ARTS-Laboratory/IoT-Water-Level-Sensor/system_development/Cellular/v0.2/Custom PCB's/Power PCB/README.md

# Power Board

These are the KiCad files used to create the power PCB.

## .SCH 
This is the electrical wiring diagram for the PCB. This file contains links to the datasheets for all components used in the PCB.

## .PCB
This is the file for creating the physical PCB (as well as offering a 3D render of the PCB)
