ARTS-Laboratory/IoT-Water-Level-Sensor/system_development/Cellular/v0.1/field tests/04_21-04_22/usgs_data.csv

 |  | date | time |  |  |  | stage | temperature
USGS | 2169000 | 4/21/2022 | 15:30 | EDT | 5.97 | 154.63 | 155 | 14.9
USGS | 2169000 | 4/21/2022 | 15:45 | EDT | 5.93 | 154.59 | 154.96 | 14.8
USGS | 2169000 | 4/21/2022 | 16:00 | EDT | 5.91 | 154.57 | 154.94 | 14.8
USGS | 2169000 | 4/21/2022 | 16:15 | EDT | 5.88 | 154.54 | 154.91 | 14.8
USGS | 2169000 | 4/21/2022 | 16:30 | EDT | 5.86 | 154.52 | 154.89 | 14.8
USGS | 2169000 | 4/21/2022 | 16:45 | EDT | 5.83 | 154.49 | 154.86 | 14.7
USGS | 2169000 | 4/21/2022 | 17:00 | EDT | 5.82 | 154.48 | 154.85 | 14.7
USGS | 2169000 | 4/21/2022 | 17:15 | EDT | 5.81 | 154.47 | 154.84 | 14.7
USGS | 2169000 | 4/21/2022 | 17:30 | EDT | 5.79 | 154.45 | 154.82 | 14.6
USGS | 2169000 | 4/21/2022 | 17:45 | EDT | 5.78 | 154.44 | 154.81 | 14.6
USGS | 2169000 | 4/21/2022 | 18:00 | EDT | 5.77 | 154.43 | 154.8 | 14.6
USGS | 2169000 | 4/21/2022 | 18:15 | EDT | 5.77 | 154.43 | 154.8 | 14.5
USGS | 2169000 | 4/21/2022 | 18:30 | EDT | 5.76 | 154.42 | 154.79 | 14.5
USGS | 2169000 | 4/21/2022 | 18:45 | EDT | 5.76 | 154.42 | 154.79 | 14.4
USGS | 2169000 | 4/21/2022 | 19:00 | EDT | 5.75 | 154.41 | 154.78 | 14.4
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
