ARTS-Laboratory/IoT-Water-Level-Sensor/system_development/Cellular/v0.1/field tests/05_03-05_09/stage_data.csv

 |  |  | date | time |  |  | value | adaptive index | adaptive value
0F0NJQPDRJXMENSYHWX61DW5M4 | 153 | 1793320 | 5/3/2022 | 9:39:42 AM | 13:39:42 | UTC | 153 | 1 | 153 | 0
0F0NJT7999G4E5HH99HHKH4P6C | 153 | 1793320 | 5/3/2022 | 9:44:07 AM | 13:44:07 | UTC | 153 | 2 | 153 | 0
0F0NJXPKSRJBQ8WAA7AC0D6Y2S | 153.25 | 1793320 | 5/3/2022 | 9:50:12 AM | 13:50:12 | UTC | 153.25 | 3 | 153.25 | 0
0F0NJZP8HF8RG365QKV08D1JWJ | 152.42 | 1793320 | 5/3/2022 | 9:53:41 AM | 13:53:41 | UTC | 152.42 | 4 | 152.42 | 0
0F0NM4R60VDQANZM3WNMMC0HX7 | 153 | 1793320 | 5/3/2022 | 10:58:27 AM | 14:58:27 | UTC | 153 | 5 | 153 | 0
0F0NM769279931YKHYYXZYRMA1 | 153 | 1793320 | 5/3/2022 | 11:02:42 AM | 15:02:42 | UTC | 153 | 6 | 153 | 0
0F0NM7P03MXMFY87XH234CH9K3 | 153 | 1793320 | 5/3/2022 | 11:03:34 AM | 15:03:34 | UTC | 153 | 7 | 153 | 0
0F0NMA3SWRW5TD514BHWAYF0Z5 | 153 | 1793320 | 5/3/2022 | 11:07:49 AM | 15:07:49 | UTC | 153 | 11 | 153 | 0
0F0NMCB0VVYKTFTS1PY2FKWZX7 | 153 | 1793320 | 5/3/2022 | 11:11:42 AM | 15:11:42 | UTC | 153 | 15 | 153 | 0
0F0NMEKFHNVDS8CANYTDE6VJWJ | 153 | 1793320 | 5/3/2022 | 11:15:40 AM | 15:15:40 | UTC | 153 | 19 | 153 | 0
0F0NMGWXJBT11FHRV2F50JVWW0 | 153 | 1793320 | 5/3/2022 | 11:19:40 AM | 15:19:40 | UTC | 153 | 23 | 153 | 0
0F0NMK5Y89X48QQDZEPRES7CVD | 153 | 1793320 | 5/3/2022 | 11:23:40 AM | 15:23:40 | UTC | 153 | 27 | 153 | 0
0F0NMNF5AP266YJV44F9623FB0 | 153 | 1793320 | 5/3/2022 | 11:27:40 AM | 15:27:40 | UTC | 153 | 31 | 153 | 0
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
0F0R3JME0WJ84MVRCA2KWJHB8K | 152.08 | 1793320 | 5/6/2022 | 1:00:42 PM | 17:00:42 | UTC | 153 |  |  | 0.92
0F0R3MXW04BC4MDB38EVNZ0SR5 | 152.08 | 1793320 | 5/6/2022 | 1:04:43 PM | 17:04:43 | UTC | 153 |  |  | 0.92
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
