ARTS-Laboratory/IoT-Water-Level-Sensor/system_development/Cellular/v0.1/field tests/05_03-05_09/usgs_data.csv

 |  | date | time |  |  | stage | temperature
USGS | 2169000 | 5/3/2022 | 9:30 | EDT | 3.97 | 153 | 15.3
USGS | 2169000 | 5/3/2022 | 9:45 | EDT | 3.97 | 153 | 15.3
USGS | 2169000 | 5/3/2022 | 10:00 | EDT | 3.97 | 153 | 15.3
USGS | 2169000 | 5/3/2022 | 10:15 | EDT | 3.97 | 153 | 15.4
USGS | 2169000 | 5/3/2022 | 10:30 | EDT | 3.97 | 153 | 15.4
USGS | 2169000 | 5/3/2022 | 10:45 | EDT | 3.97 | 153 | 15.5
USGS | 2169000 | 5/3/2022 | 11:00 | EDT | 3.97 | 153 | 15.6
USGS | 2169000 | 5/3/2022 | 11:15 | EDT | 3.97 | 153 | 15.6
USGS | 2169000 | 5/3/2022 | 11:30 | EDT | 3.97 | 153 | 15.7
USGS | 2169000 | 5/3/2022 | 11:45 | EDT | 3.97 | 153 | 15.7
USGS | 2169000 | 5/3/2022 | 12:00 | EDT | 3.97 | 153 | 15.8
USGS | 2169000 | 5/3/2022 | 12:15 | EDT | 3.97 | 153 | 15.9
USGS | 2169000 | 5/3/2022 | 12:30 | EDT | 3.97 | 153 | 16
USGS | 2169000 | 5/3/2022 | 12:45 | EDT | 3.96 | 152.99 | 16
USGS | 2169000 | 5/3/2022 | 13:00 | EDT | 3.97 | 153 | 16.1
USGS | 2169000 | 5/3/2022 | 13:15 | EDT | 3.97 | 153 | 16.1
USGS | 2169000 | 5/3/2022 | 13:30 | EDT | 3.97 | 153 | 16.2
USGS | 2169000 | 5/3/2022 | 13:45 | EDT | 3.97 | 153 | 16.2
USGS | 2169000 | 5/3/2022 | 14:00 | EDT | 3.97 | 153 | 16.3
USGS | 2169000 | 5/3/2022 | 14:15 | EDT | 3.97 | 153 | 16.3
USGS | 2169000 | 5/3/2022 | 14:30 | EDT | 3.97 | 153 | 16.4
USGS | 2169000 | 5/3/2022 | 14:45 | EDT | 3.97 | 153 | 16.4
USGS | 2169000 | 5/3/2022 | 15:00 | EDT | 3.97 | 153 | 16.4
USGS | 2169000 | 5/3/2022 | 15:15 | EDT | 3.99 | 153.02 | 16.4
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
USGS | 2169000 | 5/9/2022 | 21:00 | EDT | 2.75 | 151.78 | 16.5
USGS | 2169000 | 5/9/2022 | 21:15 | EDT | 2.76 | 151.79 | 16.5
USGS | 2169000 | 5/9/2022 | 21:30 | EDT | 2.76 | 151.79 | 16.5
USGS | 2169000 | 5/9/2022 | 21:45 | EDT | 2.77 | 151.8 | 16.5
USGS | 2169000 | 5/9/2022 | 22:00 | EDT | 2.77 | 151.8 | 16.5
USGS | 2169000 | 5/9/2022 | 22:15 | EDT | 2.78 | 151.81 | 16.5
USGS | 2169000 | 5/9/2022 | 22:30 | EDT | 2.78 | 151.81 | 16.5
USGS | 2169000 | 5/9/2022 | 22:45 | EDT | 2.78 | 151.81 | 16.5
USGS | 2169000 | 5/9/2022 | 23:00 | EDT | 2.78 | 151.81 | 16.4
USGS | 2169000 | 5/9/2022 | 23:15 | EDT | 2.78 | 151.81 | 16.4
