ARTS-Laboratory/IoT-Water-Level-Sensor/system_development/Cellular/v0.1/field tests/04_06-04_07/usgs_data.csv

 |  | date | time |  |  | stage
USGS | 2169506 | 4/6/2022 | 14:15 | EDT | 1.06 | 168.06 | P
USGS | 2169506 | 4/6/2022 | 14:30 | EDT | 1.06 | 168.06 | P
USGS | 2169506 | 4/6/2022 | 14:45 | EDT | 1.06 | 168.06 | P
USGS | 2169506 | 4/6/2022 | 15:00 | EDT | 1.05 | 168.05 | P
USGS | 2169506 | 4/6/2022 | 15:15 | EDT | 1.05 | 168.05 | P
USGS | 2169506 | 4/6/2022 | 15:30 | EDT | 1.06 | 168.06 | P
USGS | 2169506 | 4/6/2022 | 15:45 | EDT | 1.05 | 168.05 | P
USGS | 2169506 | 4/6/2022 | 16:00 | EDT | 1.06 | 168.06 | P
USGS | 2169506 | 4/6/2022 | 16:15 | EDT | 1.05 | 168.05 | P
USGS | 2169506 | 4/6/2022 | 16:30 | EDT | 1.06 | 168.06 | P
USGS | 2169506 | 4/6/2022 | 16:45 | EDT | 1.06 | 168.06 | P
USGS | 2169506 | 4/6/2022 | 17:00 | EDT | 1.06 | 168.06 | P
USGS | 2169506 | 4/6/2022 | 17:15 | EDT | 1.06 | 168.06 | P
USGS | 2169506 | 4/6/2022 | 17:30 | EDT | 1.06 | 168.06 | P
USGS | 2169506 | 4/6/2022 | 17:45 | EDT | 1.06 | 168.06 | P
USGS | 2169506 | 4/6/2022 | 18:00 | EDT | 1.05 | 168.05 | P
USGS | 2169506 | 4/6/2022 | 18:15 | EDT | 1.06 | 168.06 | P
USGS | 2169506 | 4/6/2022 | 18:30 | EDT | 1.12 | 168.12 | P
USGS | 2169506 | 4/6/2022 | 18:45 | EDT | 1.18 | 168.18 | P
USGS | 2169506 | 4/6/2022 | 19:00 | EDT | 1.23 | 168.23 | P
USGS | 2169506 | 4/6/2022 | 19:15 | EDT | 1.44 | 168.44 | P
USGS | 2169506 | 4/6/2022 | 19:30 | EDT | 1.51 | 168.51 | P
USGS | 2169506 | 4/6/2022 | 19:45 | EDT | 1.62 | 168.62 | P
USGS | 2169506 | 4/6/2022 | 20:00 | EDT | 1.96 | 168.96 | P
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
USGS | 2169506 | 4/7/2022 | 10:15 | EDT | 1.14 | 168.14 | P
USGS | 2169506 | 4/7/2022 | 10:30 | EDT | 1.13 | 168.13 | P
USGS | 2169506 | 4/7/2022 | 10:45 | EDT | 1.12 | 168.12 | P
USGS | 2169506 | 4/7/2022 | 11:00 | EDT | 1.11 | 168.11 | P
USGS | 2169506 | 4/7/2022 | 11:15 | EDT | 1.1 | 168.1 | P
